GGoodacre/WindChargeController-Capstone2024/LTSpice/Benchmark/sepic_Benchmark.asc

C1: cap; 10µF
C2: cap; 10µF
C3: cap; 10µF
C4: cap; 10µF
Cd1: cap; 10µF
Cd2: cap; 10µF
Cd3: cap; 10µF
Cd: cap; 10µF
Ci: cap; 150µ; Rser=43m
Co1: cap; 150µ; Rser=43m
Co2: cap; 150µ; Rser=43m
Co: cap; 150µ; Rser=43m
D1: diode; SBRD10200
L1: ind2; 2mH; Rser=6m
L2: ind2; 2mH; Rser=6m
M1: nmos; Si7336ADP
R1: res; 1Mega
R2: res; 5
Rd: res; 2.44
V1: voltage; 30
X1: swgen; duty=30 Freq=300k Von=5
Named nets: 0, a, b, c, d
.tran 50ms startup
K1 L1 L2 0.98
.model SBRD10200 D(Ron=1m Roff=1Meg Vfwd=0.4 Vrev=200)
Expected voltage range:
10-50V
Inductive linking coefficient between L1 and L2
Target output current ~<4A
