GGoodacre/WindChargeController-Capstone2024/LTSpice/Benchmark/totempole.asc

C1: cap; 10µ
C2: cap; 10µ
C3: cap; 10µ
L2: ind; 100n
M1: nmos; Si7336ADP
M2: nmos; Si7336ADP
M3: nmos; Si7336ADP
Q1: npn; 2N5210
Q2: pnp; 2N5087
Q3: pnp; 2N5087
Q4: npn; 2N5210
Q5: npn; 2N5210
Q6: pnp; 2N5087
R1: res; 10k
R2: res; 10k
R3: res; 1m
R4: res; 10
R5: res; 1m
R6: res; 1m
R7: res; 1m
R8: res; 100m
R9: res; 1m
R10: res; 1k
R11: res; 1m
R12: res; 10
R13: res; 10
R14: res; 10
R15: res; 1m
V1: voltage; 10
V2: voltage; 10
V3: voltage; 10
X1: swgen; duty=50 Freq=300k Von=3.3
Named nets: 0, Vout, VuC, Vbase, Vgate, Vcq3, Vbase2, Vgate2
.tran 50u
design note: R5 resistance must be very low relative to R4
assumed long distance wire
Inverting driver
non inverting driver
control
