GGoodacre/WindChargeController-Capstone2024/LTSpice/Benchmark/totempole2.asc

A1: inv
M1: nmos; Si7336ADP
M2: nmos; Si7336ADP
Q1: npn; 2N5210
Q2: pnp; 2N5087
Q3: pnp; 2N5087
R1: res; 825
R2: res; 10
R3: res; 1m
R4: res; 4k7
R6: res; 10
R7: res; 1m
V1: voltage; 5
X1: swgen; duty=50 Freq=300k Von=3.3
Named nets: 0
.tran 50u
