GGoodacre/WindChargeController-Capstone2024/LTSpice/Benchmark/DCDCtesting/sepic_Benchmark.asc

C1: cap; {C1}
Cd: cap; {Cd}
Ci: cap; {Ci}
Co: cap; {Co}
D1: diode; SBRD10200
L1: ind2; {L1}
L2: ind2; {L2}
M1: nmos; Si7336ADP
R1: res; 1Mega
R2: res; 5
Rd: res; {Rd}
V1: voltage; 60
X1: swgen; duty=30 Freq=300k Von=5
Named nets: 0, a, b, c, d
.params L1=2.333mH L2=2.333mH C1=10uF Ci=100uF Co=1000uF Cd=40uF Rd=2.44
.tran 50ms startup
K1 L1 L2 0.98
.model SBRD10200 D(Ron=1m Roff=1Meg Vfwd=0.4 Vrev=200)
