GGoodacre/WindChargeController-Capstone2024/LTSpice/WCC/windchargecontroller.asc

Battery_Req: res; 0.02
R2: res; 5
V1: voltage; 12; Rser=0
V4: voltage; 10
X1: swgen; duty=40 Freq=300k Von=5
X2: mosdrive
X5: powerswitch
X6: 3phgen; turbVolt=20 turbR=0.1 turbFreq=1000
X7: killswitch
X8: brakerectifier
X9: sepic; L1=2.333mH L2=2.333mH C1=10uF Ci=100uF Co=1000uF Cd=40uF Rd=2.44
Named nets: 0, Vout_1, Vsupply, Va, Vb, Vc, Vrect, Vdcdc, Vout_2, Vsqr, Vpwm
.tran 50ms startup
Generator hooked up in Delta
3Ph 6 pulse rectifier
Emergency electrical turbine brake 
(should not be used in normal operation)
Component sizing for SEPIC:
SEPIC topology buck/boost
Totem pole BJT mosfet driver
Generates a PWM signal
Mosfet power switcher
Tells the simulation to run for 50milliseconds
Global power supply for misc. devices
Simulated car battery
Simulated resistor dump load
