GGoodacre/WindChargeController-Capstone2024/LTSpice/WCC_lib/powerswitch.asc

U1: SCR; MCR100-003
U2: SCR; MCR100-003
U3: SCR; MCR100-003
Named nets: S1, PowerIn, Power1, S2, Power2, S3, Power3
.lib MCR100_003.lib
