GGoodacre/WindChargeController-Capstone2024/LTSpice/WCC_lib/sepic.asc

C1: cap; {C1}
Cd: cap; {Cd}
Ci: cap; {Ci}
Co: cap; {Co}
D1: diode
L1: ind2; {L1}
L2: ind2; {L2}
M1: nmos; Si7336ADP
R1: res; 1Mega
Rd: res; {Rd}
Named nets: Vin+, PWM, Vout, Vin-
.params L1=L1 L2=L2 C1=C1 Ci=Ci Co=Co Cd=Cd Rd=Rd
K1 L1 L2 0.98
diode we're using: 
SBRD10200TR
directive telling LTspice that L1 and L2 are inductively linked:
