GGoodacre/WindChargeController-Capstone2024/LTSpice/WCC_lib/mosdrive.asc

Q1: npn; 2N5210
Q2: pnp; 2N5087
R1: res; {R1}
R2: res; {R2}
Named nets: Vdrv, Vgate, Vpwm, Vref
.param R1=1m R2=1m
