GGoodacre/WindChargeController-Capstone2024/LTSpice/WCC_lib/ADC.asc

C2: cap; 10p
R1: res; 90k
R2: res; 10k
U1: AD4000
U2: OP07
Named nets: Vss, Vdd, Vmeas, Vref, V+
note that this isnt necessarily
the actual model we will use,
just a placeholder chip
