GGoodacre/WindChargeController-Capstone2024/LTSpice/WCC_lib/killswitch.asc

S1: sw; MYSW
S2: sw; MYSW
S3: sw; MYSW
Named nets: COM, Phase_A, Phase_B, Phase_C, Power
.model MYSW SW(Ron=1 Roff=10Meg Vt=0.5 Vh=-0.4)
