GGoodacre/WindChargeController-Capstone2024/LTSpice/WCC_lib/swgen.asc

V1: voltage; PULSE(0 {Von} 0 0 0 {Ton} {TPeriod})
Named nets: V+, V-
.param TPeriod = 1/Freq
.param Ton = TPeriod*duty/100
