GGoodacre/WindChargeController-Capstone2024/LTSpice/WCC_lib/3phgen.asc

V1: voltage; SINE(0 {turbVolt} {turbFreq} 0 0 0); Rser={turbR}
V2: voltage; SINE(0 {turbVolt} {turbFreq} 0 0 120); Rser={turbR}
V3: voltage; SINE(0 {turbVolt} {turbFreq} 0 0 240); Rser={turbR}
Named nets: Phase_A, Phase_B, Phase_C
.param turbVolt = turbVolt
.param turbFreq = turbFreq
.param turbR = turbR
