GGoodacre/WindChargeController-Capstone2024/LTSpice/WCC_lib/brakerectifier.asc

D1: diode; 1N914
D2: diode; 1N914
D3: diode; 1N914
M1: nmos; Si7336ADP
M2: nmos; Si7336ADP
M3: nmos; Si7336ADP
R1: res; {R1}
R2: res; {R1}
R3: res; {R1}
Named nets: Phase_A, Phase_B, Phase_C, VDC+, VDC-, Brake
.param R1 = 16
