GGoodacre/WindChargeController-Capstone2024/LTSpice/WCC_lib/buck.asc

C1: cap; 100µ
C2: cap; 100µ
D1: diode
L1: ind; 3.17µH
M1: nmos; Si7336ADP
R2: res; 2
V1: voltage; 50
V2: voltage; PULSE(0 5 0 0 0 {Ton} {Tperiod})
Named nets: 0, Vout, Vin
.param Ton = (duty/100)*Tperiod
.param Tperiod = 1/Freq
.param Freq = 1Mega
.param duty = 25
.tran 0 5ms 0
